NOAA-PMEL/EDD-LCP_Control/Firmware/LCP_Control/src/artemis/artemis_piston.c

#include "artemis_piston.h"

//*****************************************************************************
//
// Required built-ins.
//
//*****************************************************************************
#include <stdint.h>
#include <stdbool.h>
#include <string.h>
#include <stdlib.h>
#include <math.h>
#include <assert.h>
#include <stdio.h>

//*****************************************************************************
//
// Standard AmbiqSuite includes.
//
//*****************************************************************************
#include "am_mcu_apollo.h"
#include "am_bsp.h"
#include "am_util.h"

//*****************************************************************************
//
// Artemis specific files
//
//*****************************************************************************
#include "artemis_i2c.h"
#include "artemis_debug.h"
#include "artemis_stream.h"

//*****************************************************************************
//
// FreeRTOS include files.
//
//*****************************************************************************
#include "FreeRTOS.h"
#include "task.h"
#include "event_groups.h"
#include "semphr.h"


//*****************************************************************************
//
// Project Files
//
//*****************************************************************************
#include "am_bsp_pins.h"
#include "buffer_c.h"

//*****************************************************************************
//
//  Macros & Constants
//
//*****************************************************************************
#define ARTEMIS_PISTON_BUFFER_LENGTH ( 128 )

//*****************************************************************************
//
// Structs
//
//*****************************************************************************
typedef uint8_t module_buffer_t[ARTEMIS_PISTON_BUFFER_LENGTH];
typedef struct s_module_t
{
    artemis_i2c_t i2c;
    module_buffer_t txbuffer;
    module_buffer_t rxbuffer;
    struct {
        uint32_t pin;
        am_hal_gpio_pincfg_t *pinConfig;
    }power;
} module_t;

//*****************************************************************************
//
// Static Variables
//
//*****************************************************************************
/**
 * @brief Module Parameters
 * 
 */
static module_t module;

//*****************************************************************************
//
// Static Function Prototypes
//
//*****************************************************************************


//*****************************************************************************
//
// Global Functions
//
//*****************************************************************************
void artemis_piston_i2c_initialize(uint8_t i2c_addr)
{
    artemis_i2c_t *i2c = &module.i2c;
    module.power.pinConfig = (am_hal_gpio_pincfg_t *)&g_AM_BSP_GPIO_GPS_ON;
    module.power.pin = AM_BSP_GPIO_PWR_CTRL_EN;
    


    i2c->address = i2c_addr;
    i2c->iom.module = 2;
    i2c->iom.config.eInterfaceMode = AM_HAL_IOM_I2C_MODE;
    i2c->iom.config.ui32ClockFreq = AM_HAL_IOM_400KHZ;
    artemis_iom_initialize(&i2c->iom);

    ARTEMIS_DEBUG_HALSTATUS(am_hal_gpio_pinconfig(module.power.pin, *module.power.pinConfig));
    artemis_piston_i2c_power_off();
    am_hal_systick_delay_us(1000);
    artemis_piston_i2c_power_on();


    ARTEMIS_DEBUG_HALSTATUS(am_hal_gpio_pinconfig(AM_BSP_GPIO_IOM2_SCL, g_AM_BSP_GPIO_IOM2_SCL));
    ARTEMIS_DEBUG_HALSTATUS(am_hal_gpio_pinconfig(AM_BSP_GPIO_IOM2_SDA, g_AM_BSP_GPIO_IOM2_SDA));
    

}

void artemis_piston_i2c_power_on(void)
{
    am_hal_gpio_state_write(module.power.pin, AM_HAL_GPIO_OUTPUT_SET);
}

void artemis_piston_i2c_power_off(void)
{
    am_hal_gpio_state_write(module.power.pin, AM_HAL_GPIO_OUTPUT_CLEAR);
}

void artemis_piston_i2c_send_msg(uint8_t *msg, uint16_t len, bool stop)
{
  
  
    artemis_i2c_t *i2c = &module.i2c;
  artemis_stream_t txstream = {0};
  artemis_stream_setbuffer(&txstream, module.txbuffer, ARTEMIS_PISTON_BUFFER_LENGTH);
  artemis_stream_reset(&txstream);
  
  while(len > 0)
  {
    if(len > ARTEMIS_PISTON_BUFFER_LENGTH)
    {
      artemis_stream_write(&txstream, msg, ARTEMIS_PISTON_BUFFER_LENGTH);
      artemis_i2c_send(i2c, false, &txstream);
      artemis_stream_reset(&txstream);
      len -= ARTEMIS_PISTON_BUFFER_LENGTH;
    } else {
      artemis_stream_write(&txstream, msg, len);
      artemis_i2c_send(i2c, stop, &txstream);
      len =0;
    }
  }
  
//  while(len-- > 0)
//  {
//    artemis_stream_reset(&txstream);
//    artemis_stream_write(&txstream, msg++, 1);
//    if(len > 0)
//    {
//        artemis_i2c_send(i2c, false, &txstream);
//    } else {
//      artemis_i2c_send(i2c, stop, &txstream);
//    }
//  }
}

// uint16_t artemis_piston_i2c_read_data(uint8_t *pBuf)
// {
//     artemis_i2c_t *i2c = &module.i2c;

//     artemis_stream_t rxstream = {0};
//     artemis_stream_t txstream = {0};
//     artemis_stream_setbuffer(&rxstream, module.rxbuffer, ARTEMIS_PISTON_BUFFER_LENGTH);
//     artemis_stream_setbuffer(&txstream, module.txbuffer, ARTEMIS_PISTON_BUFFER_LENGTH);

//     /** Send the command to retreive data length @addr 0xFD */
//     artemis_stream_put(&txstream, ARTEMIS_PISTON_BUFFER_LENGTH);
//     artemis_i2c_send(i2c, false, &txstream);

//     artemis_i2c_receive(i2c, true, &rxstream, 2);

//     uint8_t u8Len[2];
//     artemis_stream_read(&rxstream, u8Len, 2);


//     if(u8Len[1] == 0xFF)
//     {
//         /** Error, shouldn't be 0xFF */
//         return 0;
//     }

//     uint16_t len = (u8Len[0] << 8) | u8Len[1];
//     //  printf("aui2c len = %u\n\n", len);
//     uint8_t *pBufStart = pBuf;

//     if(len > 0)
//     {
//     artemis_stream_reset(&txstream);
//     artemis_stream_reset(&rxstream);

//     /** Send the command to retreive data @addr 0xFF */
//     artemis_stream_put(&txstream, ARTEMIS_UBLOX_I2C_DATA_REG);
//     artemis_i2c_send(i2c, false, &txstream);

//     while(len > 0)
//     {
//         if(len > ARTEMIS_UBLOX_BUFFER_LENGTH)
//         {
//             artemis_i2c_receive(i2c, false, &rxstream, ARTEMIS_UBLOX_BUFFER_LENGTH);
//             artemis_stream_read(&rxstream, pBuf, ARTEMIS_UBLOX_BUFFER_LENGTH);
//             artemis_stream_reset(&rxstream);
//             pBuf += ARTEMIS_UBLOX_BUFFER_LENGTH;
//             len -= ARTEMIS_UBLOX_BUFFER_LENGTH;
//         } else {
//             artemis_i2c_receive(i2c, true, &rxstream, len);
//             artemis_stream_read(&rxstream, pBuf, ARTEMIS_UBLOX_BUFFER_LENGTH);
//             pBuf += len;
//             len = 0;
//         }
//     }

//     }

// return (uint16_t)(pBuf - pBufStart);

// }

void artemis_piston_i2c_read(uint8_t addr, uint8_t *data, uint8_t len)
{
    artemis_i2c_t *i2c = &module.i2c;

    artemis_stream_t rxstream = {0};
    artemis_stream_t txstream = {0};
    artemis_stream_setbuffer(&rxstream, module.rxbuffer, ARTEMIS_PISTON_BUFFER_LENGTH);
    artemis_stream_setbuffer(&txstream, module.txbuffer, ARTEMIS_PISTON_BUFFER_LENGTH);

    /** Send the command to retreive data length @addr 0xFD */
    artemis_stream_put(&txstream, ARTEMIS_PISTON_BUFFER_LENGTH);
    artemis_i2c_send(i2c, false, &txstream);

    artemis_i2c_receive(i2c, true, &rxstream, len);

    artemis_stream_read(&rxstream, data, len);
}


void artemis_piston_set_write_mode(bool state)
{
  uint8_t key = 0x00;
  uint8_t msg[2] = {0x07, 0x00};
  if(state)
  {
    key = 0xA5;
  }
  msg[1] = key;
  
  artemis_piston_i2c_send_msg(msg, 1, false);
  artemis_piston_i2c_send_msg(msg, 2, true);
  am_hal_systick_delay_us(500000);
}
